Hasenpups/WLED_All-in-one_Controller/Images/IMG_8540.JPEG

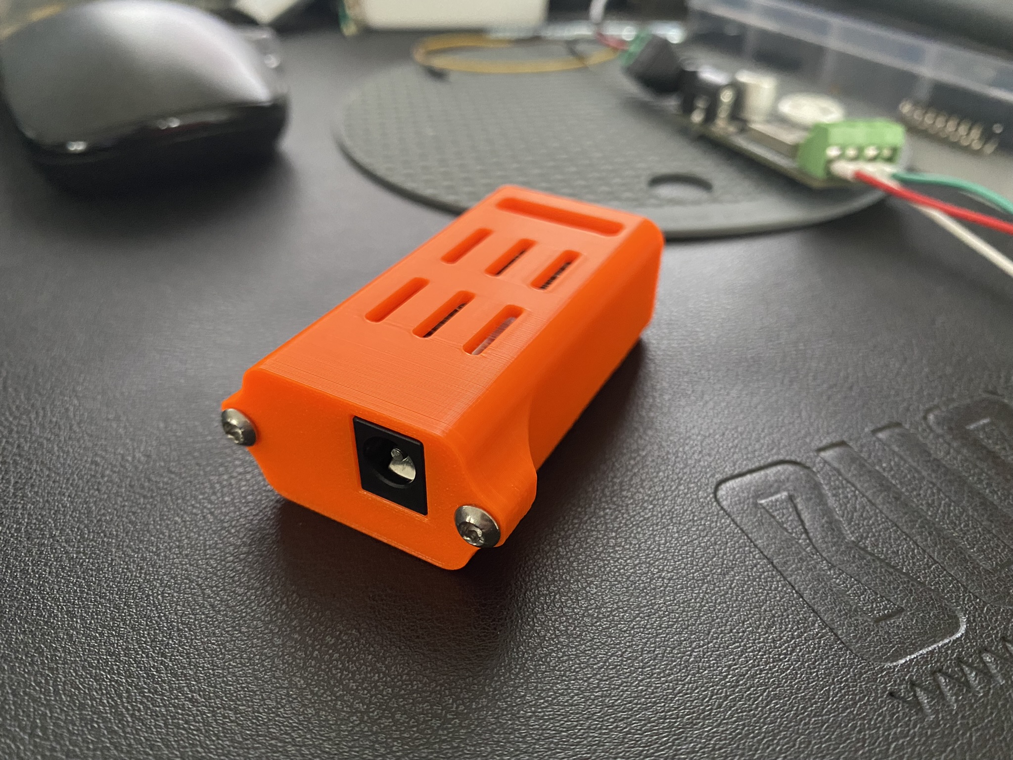
Images/IMG_8540.JPEG
