Hasenpups/WLED_All-in-one_Controller/Images/IMG_8541.JPEG

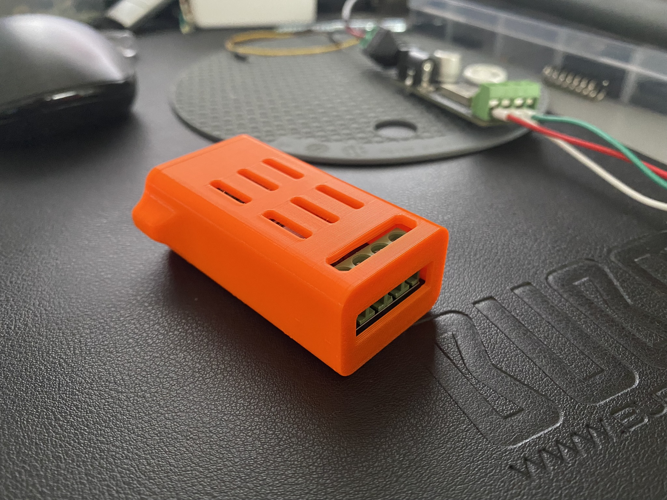
Images/IMG_8541.JPEG
